skurella/nixie/software/MCUtest.X/encoder.h

/* 
 * File:   encoder.h
 * Author: Sebastian Kurella
 *
 * Created on 17.06.2015, 11:48
 */

#ifndef ENCODER_H
#define	ENCODER_H

#ifdef	__cplusplus
extern "C" {
#endif


#define ENCODER_STATE_DENT      0
#define ENCODER_STATE_BEGINCW   1
#define ENCODER_STATE_MIDCW     2
#define ENCODER_STATE_ENDCW     3
#define ENCODER_STATE_BEGINCCW  4
#define ENCODER_STATE_MIDCCW    5
#define ENCODER_STATE_ENDCCW    6

#define ENCODER_TURN_NOTURN             0
#define ENCODER_TURN_CLOCKWISE          1
#define ENCODER_TURN_COUNTERCLOCKWISE   2

extern volatile char ENCODER_STATE;

// Init encoder inputs
void encoder_init();

// Returns encoder state machine state
inline unsigned char encoder_getState();

// Sets encoder state machine state
inline void encoder_setState(unsigned char state);

// Updates encoder state machine
// Return values:
// 0 - no change
// 1 - clockwise turn
// 2 - counterclockwise turn
unsigned char encoder_updateState();


#ifdef	__cplusplus
}
#endif

#endif	/* ENCODER_H */
