skurella/nixie/software/MCUtest.X/peripherals.h

/* 
 * File:   peripherals.h
 * Author: Sebastian Kurella
 *
 * Created on 30.06.2015, 14:18
 */

#ifndef PERIPHERALS_H
#define	PERIPHERALS_H

#ifdef	__cplusplus
extern "C" {
#endif

// Init peripherals
void peripherals_init();

inline void buzzer_on();
inline void buzzer_off();

inline void blue_led_on();
inline void blue_led_off();

inline void red_led_on();
inline void red_led_off();

inline char encoder_button_state();

inline char button_state();


#ifdef	__cplusplus
}
#endif

#endif	/* PERIPHERALS_H */
